Leeianiop/WatchBlocks/Images/WBWR.png

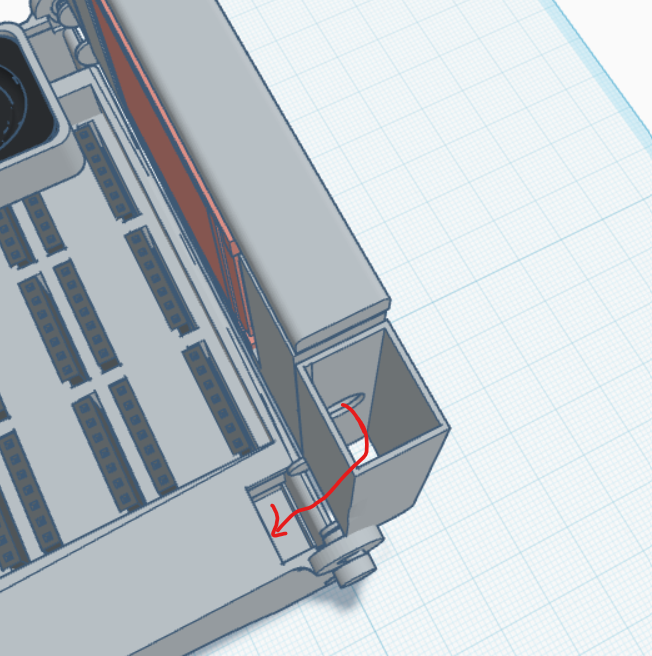
Images/WBWR.png
