Leeianiop/WatchBlocks/WatchBlocksCAD1/WatchBlocksTemplate.stl

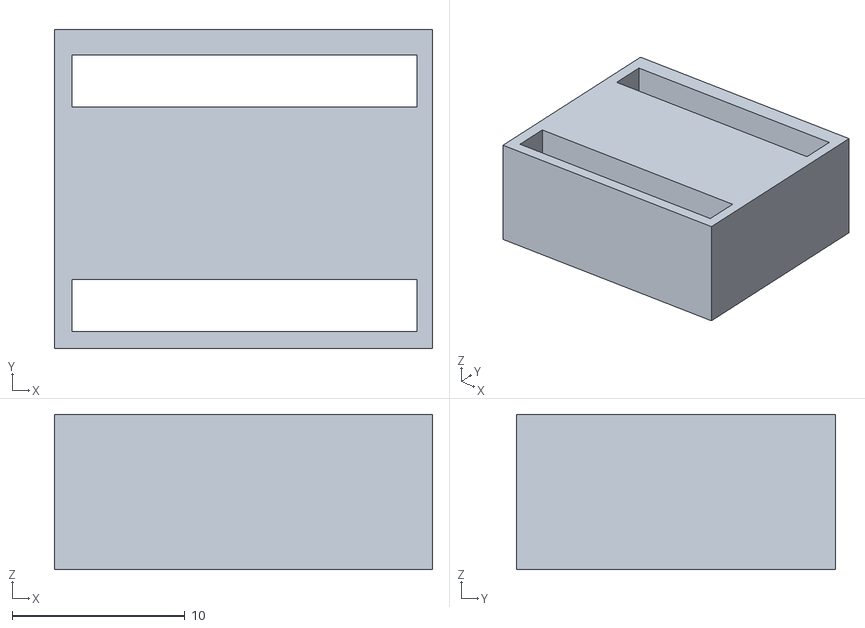
[picture p43: CAD file, 2026-06-20]
WatchBlocksCAD1/WatchBlocksTemplate.stl
21.9 x 18.5 x 9.00
