Leeianiop/WatchBlocks/WatchBlocksCAD1/WatchBlocksScrew.stl

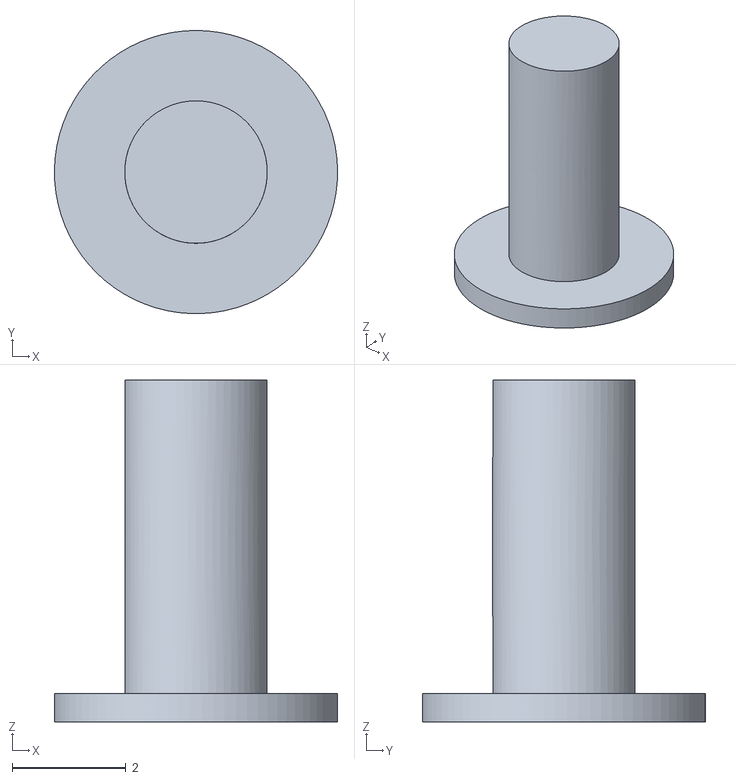
[picture p44: CAD file, 2026-06-24]
WatchBlocksCAD1/WatchBlocksScrew.stl
4.97 x 4.97 x 6.00
