Leeianiop/WatchBlocks/WatchBlocksPCB1/WatchBlocksSCH.kicad_sch

## KiCad design WatchBlocksPCB1/WatchBlocksSCH.kicad_sch (2026-06-24)

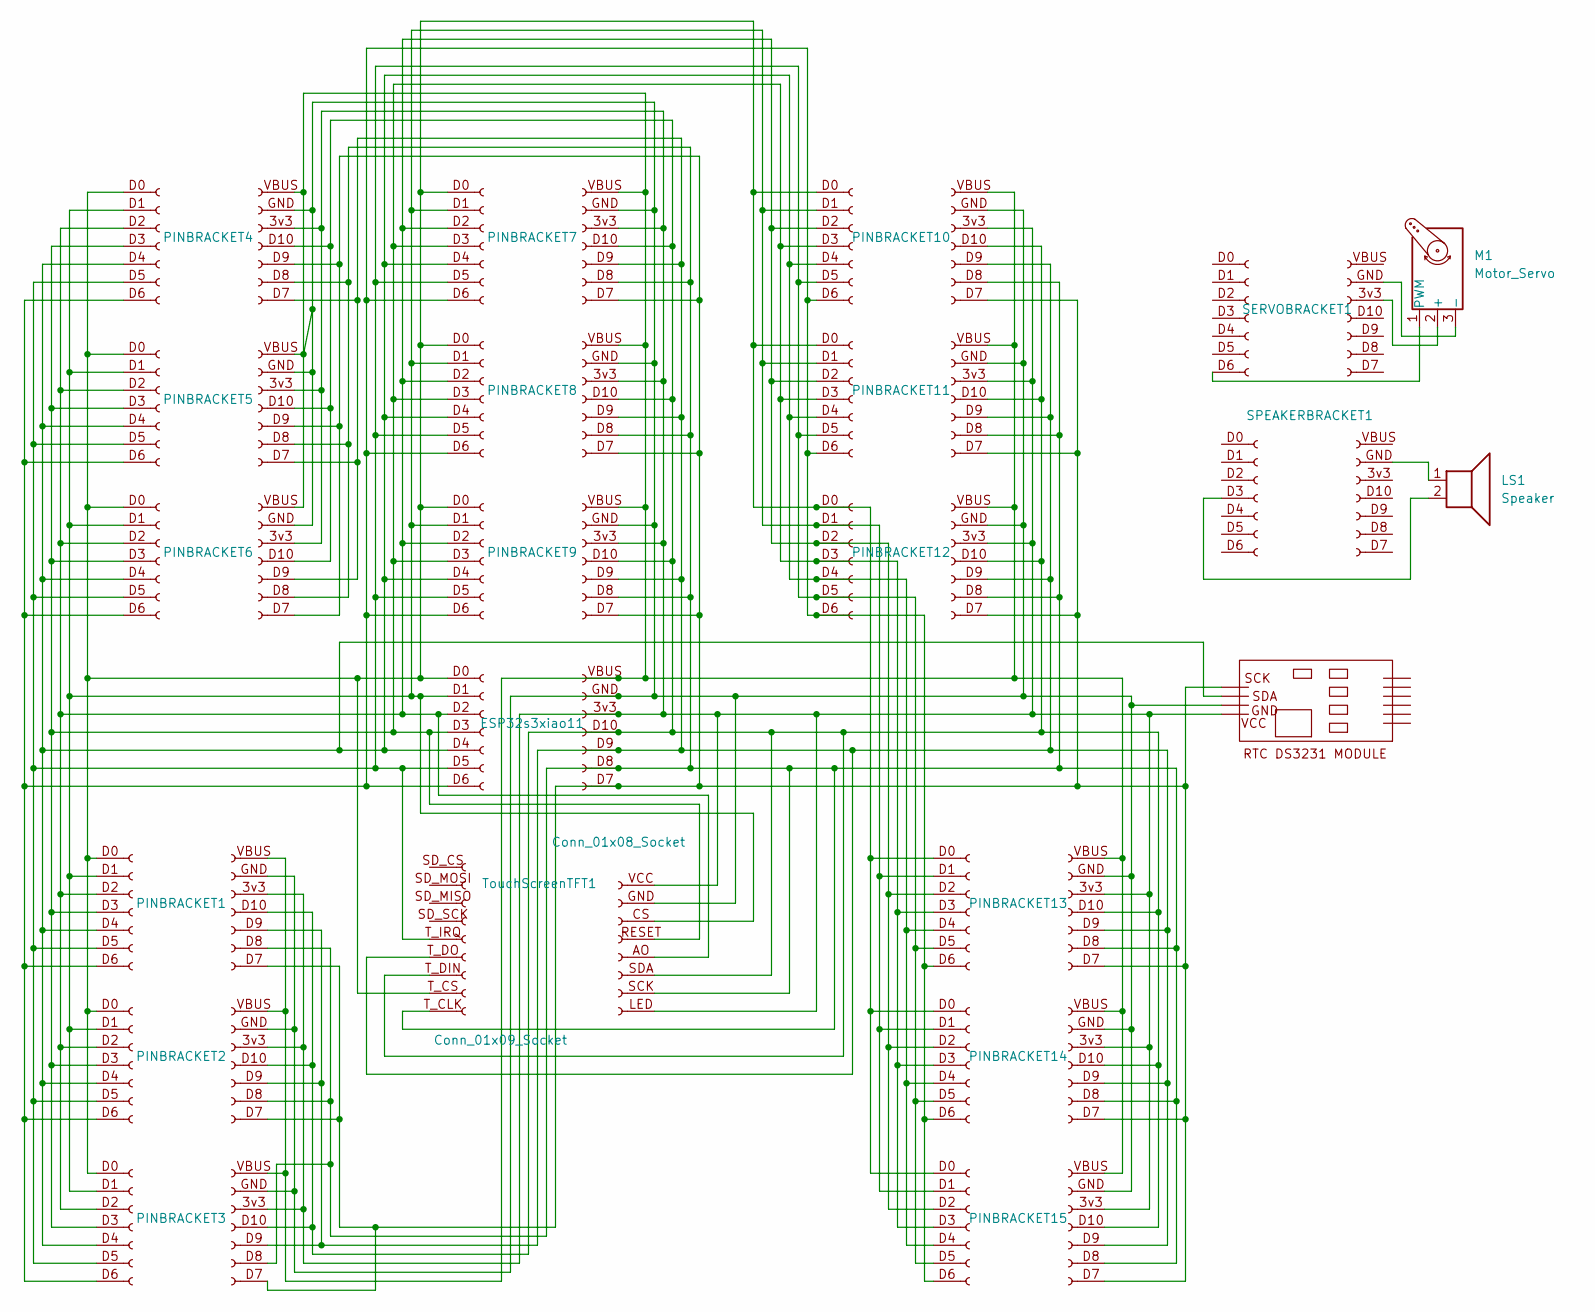
[picture p45: schematic WatchBlocksSCH.kicad_sch]

Parts:
ESP32S3XIAO1, ESP32S3XIAO2, ESP32S3XIAO3, ESP32S3XIAO4, ESP32S3XIAO5, ESP32S3XIAO6, ESP32S3XIAO7, ESP32S3XIAO8, ESP32S3XIAO9, ESP32S3XIAO10, ESP32S3XIAO12, ESP32S3XIAO13, ESP32S3XIAO14, ESP32S3XIAO15, ESP32S3XIAO16, ESP32S3XIAO17, ESP32s3xiao11: Conn_01x07_Socket; PinSocket_1x07_P2.54mm_Vertical
ESP32S3XIAO18, ESP32S3XIAO19: Conn_01x07_Socket; PinHeader_1x07_P2.54mm_Vertical
J1: Conn_01x09_Socket
LS1: Speaker
M1: Motor_Servo; PinHeader_1x03_P2.54mm_Vertical
PINBRACKET1, PINBRACKET2, PINBRACKET3, PINBRACKET4, PINBRACKET5, PINBRACKET6, PINBRACKET7, PINBRACKET8, PINBRACKET9, PINBRACKET10, PINBRACKET11, PINBRACKET12, PINBRACKET13, PINBRACKET14, PINBRACKET15: Conn_01x07_Socket; PinSocket_1x07_P2.54mm_Vertical
SERVOBRACKET1: Conn_01x07_Socket; PinHeader_1x07_P2.54mm_Vertical
SPEAKERBRACKET1: Conn_01x07_Socket; PinHeader_1x07_P2.54mm_Vertical
TouchScreenTFT1: Conn_01x08_Socket
U2: (no value)

Connections:
unnamed: ESP32S3XIAO1.D0 (Pin_1), ESP32S3XIAO2.D0 (Pin_1), ESP32S3XIAO3.D0 (Pin_1), ESP32S3XIAO4.D0 (Pin_1), ESP32S3XIAO5.D0 (Pin_1), ESP32S3XIAO6.D0 (Pin_1), ESP32S3XIAO7.D0 (Pin_1), ESP32S3XIAO8.D0 (Pin_1), ESP32S3XIAO9.D0 (Pin_1), ESP32S3XIAO10.D0 (Pin_1), ESP32S3XIAO12.D0 (Pin_1), ESP32S3XIAO13.D0 (Pin_1), ESP32S3XIAO14.D0 (Pin_1), ESP32S3XIAO15.D0 (Pin_1), ESP32S3XIAO16.D0 (Pin_1), ESP32S3XIAO17.D0 (Pin_1), J1.T_CS (Pin_8)
unnamed: ESP32S3XIAO1.D1 (Pin_2), ESP32S3XIAO2.D1 (Pin_2), ESP32S3XIAO3.D1 (Pin_2), ESP32S3XIAO4.D1 (Pin_2), ESP32S3XIAO5.D1 (Pin_2), ESP32S3XIAO6.D1 (Pin_2), ESP32S3XIAO7.D1 (Pin_2), ESP32S3XIAO8.D1 (Pin_2), ESP32S3XIAO9.D1 (Pin_2), ESP32S3XIAO10.D1 (Pin_2), ESP32S3XIAO12.D1 (Pin_2), ESP32S3XIAO13.D1 (Pin_2), ESP32S3XIAO14.D1 (Pin_2), ESP32S3XIAO15.D1 (Pin_2), ESP32S3XIAO16.D1 (Pin_2), ESP32S3XIAO17.D1 (Pin_2), TouchScreenTFT1.CS (Pin_6)
unnamed: ESP32S3XIAO1.D2 (Pin_3), ESP32S3XIAO2.D2 (Pin_3), ESP32S3XIAO3.D2 (Pin_3), ESP32S3XIAO4.D2 (Pin_3), ESP32S3XIAO5.D2 (Pin_3), ESP32S3XIAO6.D2 (Pin_3), ESP32S3XIAO7.D2 (Pin_3), ESP32S3XIAO8.D2 (Pin_3), ESP32S3XIAO9.D2 (Pin_3), ESP32S3XIAO10.D2 (Pin_3), ESP32S3XIAO12.D2 (Pin_3), ESP32S3XIAO13.D2 (Pin_3), ESP32S3XIAO14.D2 (Pin_3), ESP32S3XIAO15.D2 (Pin_3), ESP32S3XIAO16.D2 (Pin_3), ESP32S3XIAO17.D2 (Pin_3), TouchScreenTFT1.AO (Pin_4)
unnamed: ESP32S3XIAO1.D3 (Pin_4), ESP32S3XIAO2.D3 (Pin_4), ESP32S3XIAO3.D3 (Pin_4), ESP32S3XIAO4.D3 (Pin_4), ESP32S3XIAO5.D3 (Pin_4), ESP32S3XIAO6.D3 (Pin_4), ESP32S3XIAO7.D3 (Pin_4), ESP32S3XIAO8.D3 (Pin_4), ESP32S3XIAO9.D3 (Pin_4), ESP32S3XIAO10.D3 (Pin_4), ESP32S3XIAO12.D3 (Pin_4), ESP32S3XIAO13.D3 (Pin_4), ESP32S3XIAO14.D3 (Pin_4), ESP32S3XIAO15.D3 (Pin_4), ESP32S3XIAO16.D3 (Pin_4), ESP32S3XIAO17.D3 (Pin_4), TouchScreenTFT1.RESET (Pin_5)
unnamed: ESP32S3XIAO1.D4 (Pin_5), ESP32S3XIAO2.D4 (Pin_5), ESP32S3XIAO3.D4 (Pin_5), ESP32S3XIAO4.D4 (Pin_5), ESP32S3XIAO5.D4 (Pin_5), ESP32S3XIAO6.D4 (Pin_5), ESP32S3XIAO7.D4 (Pin_5), ESP32S3XIAO8.D4 (Pin_5), ESP32S3XIAO9.D4 (Pin_5), ESP32S3XIAO10.D4 (Pin_5), ESP32S3XIAO12.D4 (Pin_5), ESP32S3XIAO13.D4 (Pin_5), ESP32S3XIAO14.D4 (Pin_5), ESP32S3XIAO15.D4 (Pin_5), ESP32S3XIAO16.D4 (Pin_5), ESP32S3XIAO17.D4 (Pin_5), U2.
unnamed: ESP32S3XIAO1.D5 (Pin_6), ESP32S3XIAO2.D5 (Pin_6), ESP32S3XIAO3.D5 (Pin_6), ESP32S3XIAO4.D5 (Pin_6), ESP32S3XIAO5.D5 (Pin_6), ESP32S3XIAO6.D5 (Pin_6), ESP32S3XIAO7.D5 (Pin_6), ESP32S3XIAO8.D5 (Pin_6), ESP32S3XIAO9.D5 (Pin_6), ESP32S3XIAO10.D5 (Pin_6), ESP32S3XIAO12.D5 (Pin_6), ESP32S3XIAO13.D5 (Pin_6), ESP32S3XIAO14.D5 (Pin_6), ESP32S3XIAO15.D5 (Pin_6), ESP32S3XIAO16.D5 (Pin_6), ESP32S3XIAO17.D5 (Pin_6), J1.T_IRQ (Pin_5)
unnamed: ESP32S3XIAO1.D6 (Pin_7), ESP32S3XIAO2.D6 (Pin_7), ESP32S3XIAO3.D6 (Pin_7), ESP32S3XIAO4.D6 (Pin_7), ESP32S3XIAO5.D6 (Pin_7), ESP32S3XIAO6.D6 (Pin_7), ESP32S3XIAO7.D6 (Pin_7), ESP32S3XIAO8.D6 (Pin_7), ESP32S3XIAO9.D6 (Pin_7), ESP32S3XIAO10.D6 (Pin_7), ESP32S3XIAO12.D6 (Pin_7), ESP32S3XIAO13.D6 (Pin_7), ESP32S3XIAO14.D6 (Pin_7), ESP32S3XIAO15.D6 (Pin_7), ESP32S3XIAO16.D6 (Pin_7), ESP32S3XIAO17.D6 (Pin_7)
unnamed: ESP32S3XIAO18.D6 (Pin_7), M1.1 (PWM)
unnamed: ESP32S3XIAO19.D3 (Pin_4), LS1.2
unnamed: ESP32s3xiao11.3v3 (Pin_5), PINBRACKET1.3v3 (Pin_5), PINBRACKET2.3v3 (Pin_5), PINBRACKET3.3v3 (Pin_5), PINBRACKET4.3v3 (Pin_5), PINBRACKET5.3v3 (Pin_5), PINBRACKET6.3v3 (Pin_5), PINBRACKET7.3v3 (Pin_5), PINBRACKET8.3v3 (Pin_5), PINBRACKET9.3v3 (Pin_5), PINBRACKET10.3v3 (Pin_5), PINBRACKET11.3v3 (Pin_5), PINBRACKET12.3v3 (Pin_5), PINBRACKET13.3v3 (Pin_5), PINBRACKET14.3v3 (Pin_5), PINBRACKET15.3v3 (Pin_5), TouchScreenTFT1.LED (Pin_1), TouchScreenTFT1.VCC (Pin_8), U2.
unnamed: ESP32s3xiao11.D7 (Pin_1), PINBRACKET1.D7 (Pin_1), PINBRACKET2.D7 (Pin_1), PINBRACKET3.D7 (Pin_1), PINBRACKET4.D9 (Pin_3), PINBRACKET5.D9 (Pin_3), PINBRACKET6.D7 (Pin_1), PINBRACKET7.D7 (Pin_1), PINBRACKET8.D7 (Pin_1), PINBRACKET9.D7 (Pin_1), PINBRACKET10.D7 (Pin_1), PINBRACKET11.D7 (Pin_1), PINBRACKET12.D7 (Pin_1), PINBRACKET13.D7 (Pin_1), PINBRACKET14.D7 (Pin_1), PINBRACKET15.D7 (Pin_1), U2.
unnamed: ESP32s3xiao11.D8 (Pin_2), J1.T_CLK (Pin_9), PINBRACKET1.D8 (Pin_2), PINBRACKET2.D8 (Pin_2), PINBRACKET3.D8 (Pin_2), PINBRACKET4.D8 (Pin_2), PINBRACKET5.D8 (Pin_2), PINBRACKET6.D8 (Pin_2), PINBRACKET7.D8 (Pin_2), PINBRACKET8.D8 (Pin_2), PINBRACKET9.D8 (Pin_2), PINBRACKET10.D8 (Pin_2), PINBRACKET11.D8 (Pin_2), PINBRACKET12.D8 (Pin_2), PINBRACKET13.D8 (Pin_2), PINBRACKET14.D8 (Pin_2), PINBRACKET15.D8 (Pin_2), TouchScreenTFT1.SCK (Pin_2)
unnamed: ESP32s3xiao11.D9 (Pin_3), J1.T_DO (Pin_6), PINBRACKET1.D9 (Pin_3), PINBRACKET2.D9 (Pin_3), PINBRACKET3.D9 (Pin_3), PINBRACKET4.D7 (Pin_1), PINBRACKET5.D7 (Pin_1), PINBRACKET6.D9 (Pin_3), PINBRACKET7.D9 (Pin_3), PINBRACKET8.D9 (Pin_3), PINBRACKET9.D9 (Pin_3), PINBRACKET10.D9 (Pin_3), PINBRACKET11.D9 (Pin_3), PINBRACKET12.D9 (Pin_3), PINBRACKET13.D9 (Pin_3), PINBRACKET14.D9 (Pin_3), PINBRACKET15.D9 (Pin_3)
unnamed: ESP32s3xiao11.D10 (Pin_4), J1.T_DIN (Pin_7), PINBRACKET1.D10 (Pin_4), PINBRACKET2.D10 (Pin_4), PINBRACKET3.D10 (Pin_4), PINBRACKET4.D10 (Pin_4), PINBRACKET5.D10 (Pin_4), PINBRACKET6.D10 (Pin_4), PINBRACKET7.D10 (Pin_4), PINBRACKET8.D10 (Pin_4), PINBRACKET9.D10 (Pin_4), PINBRACKET10.D10 (Pin_4), PINBRACKET11.D10 (Pin_4), PINBRACKET12.D10 (Pin_4), PINBRACKET13.D10 (Pin_4), PINBRACKET14.D10 (Pin_4), PINBRACKET15.D10 (Pin_4), TouchScreenTFT1.SDA (Pin_3)
unnamed: ESP32s3xiao11.GND (Pin_6), ESP32s3xiao11.VBUS (Pin_7), PINBRACKET1.GND (Pin_6), PINBRACKET1.VBUS (Pin_7), PINBRACKET2.GND (Pin_6), PINBRACKET2.VBUS (Pin_7), PINBRACKET3.GND (Pin_6), PINBRACKET3.VBUS (Pin_7), PINBRACKET4.GND (Pin_6), PINBRACKET4.VBUS (Pin_7), PINBRACKET5.GND (Pin_6), PINBRACKET5.VBUS (Pin_7), PINBRACKET6.GND (Pin_6), PINBRACKET6.VBUS (Pin_7), PINBRACKET7.GND (Pin_6), PINBRACKET7.VBUS (Pin_7), PINBRACKET8.GND (Pin_6), PINBRACKET8.VBUS (Pin_7), PINBRACKET9.GND (Pin_6), PINBRACKET9.VBUS (Pin_7), PINBRACKET10.GND (Pin_6), PINBRACKET10.VBUS (Pin_7), PINBRACKET11.GND (Pin_6), PINBRACKET11.VBUS (Pin_7), PINBRACKET12.GND (Pin_6), PINBRACKET12.VBUS (Pin_7), PINBRACKET13.GND (Pin_6), PINBRACKET13.VBUS (Pin_7), PINBRACKET14.GND (Pin_6), PINBRACKET14.VBUS (Pin_7), PINBRACKET15.GND (Pin_6), PINBRACKET15.VBUS (Pin_7), TouchScreenTFT1.GND (Pin_7), U2.
unnamed: LS1.1, SPEAKERBRACKET1.GND (Pin_6)
unnamed: M1.2 (+), SERVOBRACKET1.3v3 (Pin_5)
unnamed: M1.3 (-), SERVOBRACKET1.GND (Pin_6)
